TheRetroWeb/PicoPOST/firmware/src/bitmaps.hpp

#ifndef PICOPOST_BITMAP_HPP
#define PICOPOST_BITMAP_HPP

#include "common.hpp"

static const Icon bmp_empty = {
    c_ui_iconSize, c_ui_iconSize,
    { 0x00, 0x00, 0x00, 0x00, 0x00, 0x00, 0x00, 0x00 }
};

static const Icon bmp_arrowUp = {
    c_ui_iconSize, c_ui_iconSize,
    { 0x08, 0x1C, 0x1C, 0x1C, 0x3E, 0x3E, 0x3E, 0x7F }
};

static const Icon bmp_arrowDown = {
    c_ui_iconSize, c_ui_iconSize,
    { 0x7F, 0x3E, 0x3E, 0x3E, 0x1C, 0x1C, 0x1C, 0x08 }
};

static const Icon bmp_select = {
    c_ui_iconSize, c_ui_iconSize,
    { 0x00, 0x40, 0x40, 0x44, 0x46, 0x7F, 0x06, 0x04 }
};

static const Icon bmp_back = {
    c_ui_iconSize, c_ui_iconSize,
    { 0x00, 0x0E, 0x01, 0x21, 0x61, 0xFE, 0x60, 0x20 }
};

static const Icon bmp_picoPost = {
    88, 32,
    { 0x7F, 0xFF, 0xFF, 0xFF, 0xFF, 0xFF, 0xFF, 0xFF, 0xFF, 0xFF, 0x00,
        0xB6, 0xDB, 0x6D, 0xB6, 0xDB, 0x6D, 0xB6, 0xDB, 0x6D, 0xB6, 0x80,
        0xB6, 0xDB, 0x6D, 0xB6, 0xDB, 0x6D, 0xB6, 0xDB, 0x6D, 0xB6, 0x80,
        0xA4, 0x92, 0x49, 0x24, 0x92, 0x49, 0x24, 0x92, 0x49, 0x24, 0x80,
        0x80, 0x00, 0x00, 0x00, 0x00, 0x00, 0x00, 0x00, 0x00, 0x00, 0x80,
        0x87, 0xFF, 0xBD, 0xFC, 0xEF, 0xE0, 0x00, 0x00, 0x00, 0x00, 0x80,
        0xB0, 0x00, 0x00, 0x00, 0x00, 0x00, 0x00, 0x00, 0x00, 0x0C, 0x80,
        0xB0, 0x00, 0x00, 0x00, 0x00, 0x00, 0x00, 0x0F, 0xE0, 0x0C, 0x80,
        0x80, 0x00, 0x00, 0x00, 0x3F, 0xFF, 0x00, 0x10, 0x10, 0x00, 0x80,
        0x80, 0x00, 0x00, 0x00, 0x20, 0x01, 0x00, 0x17, 0xD0, 0x7F, 0x80,
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
            0xFC, 0xFF, 0x78,
            0xF3, 0xFE, 0xB8,
            0xFF, 0xFD, 0x78,
            0x3F, 0xFA, 0xF8,
            0x8F, 0xFF, 0xF8,
            0x87, 0xFF, 0xF0,
            0x77, 0xC6, 0xE0,
            0x77, 0xDE, 0xB7,
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
};

#endif // PICOPOST_BITMAP_HPP
